breakintoprogram/pico-mposite/images/breadboard.jpeg

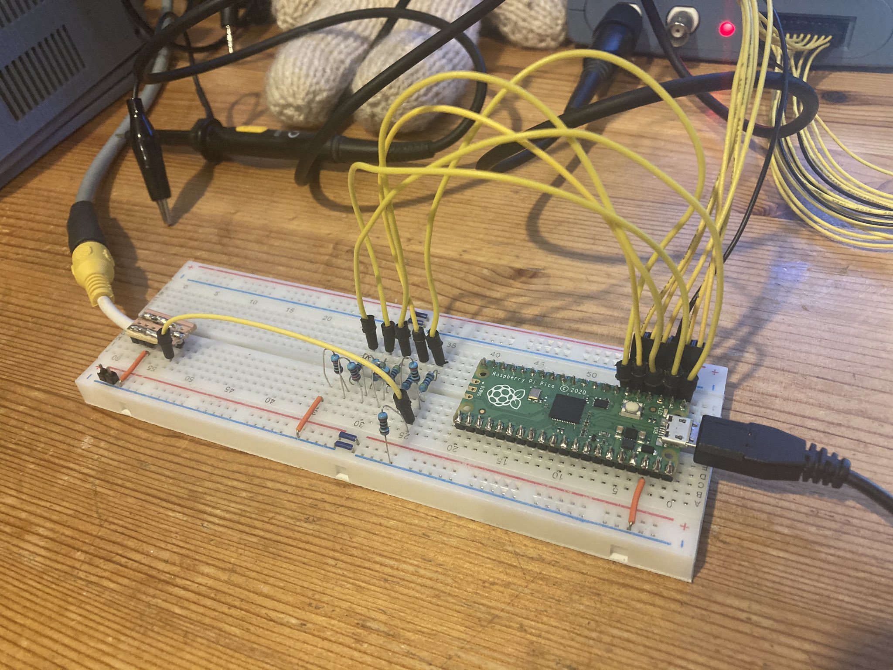
images/breadboard.jpeg
