breakintoprogram/pico-mposite/images/demo_cube.jpeg

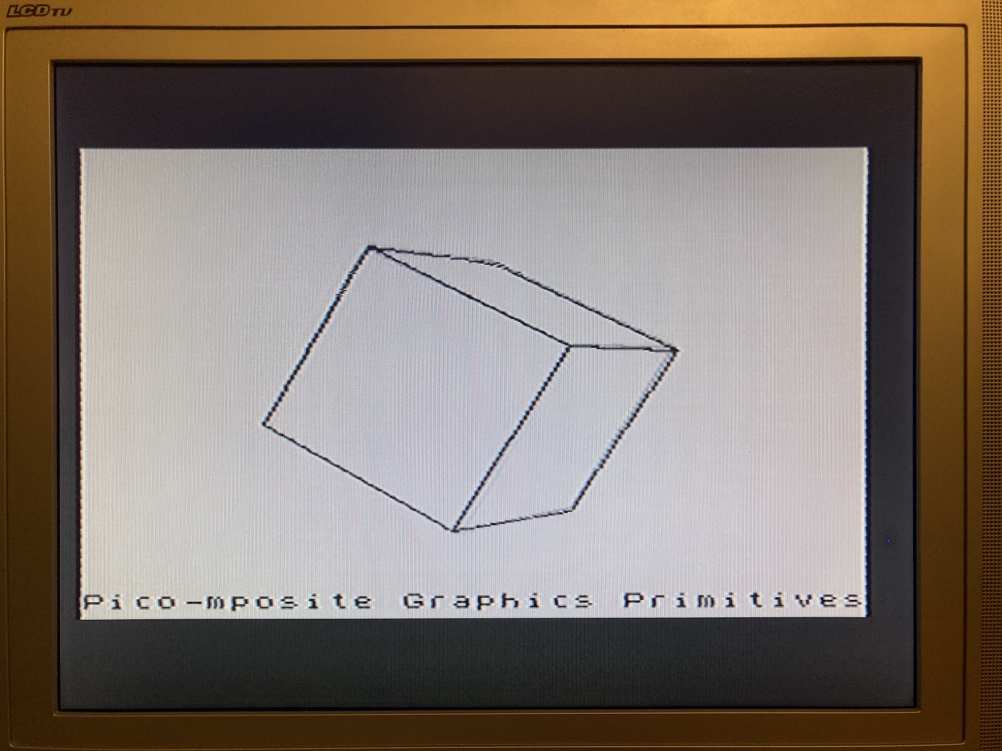
images/demo_cube.jpeg
