breakintoprogram/pico-mposite/images/demo_mandlebrot.jpeg

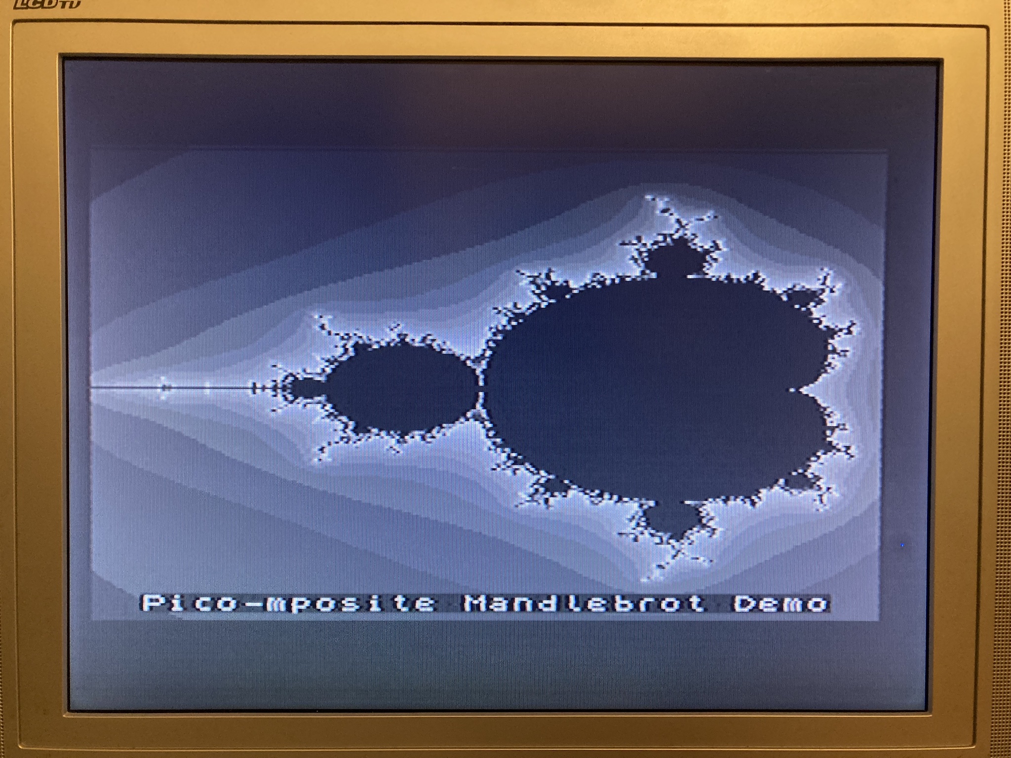
images/demo_mandlebrot.jpeg
