breakintoprogram/pico-mposite/images/demo_mandlebrot_colour.jpeg

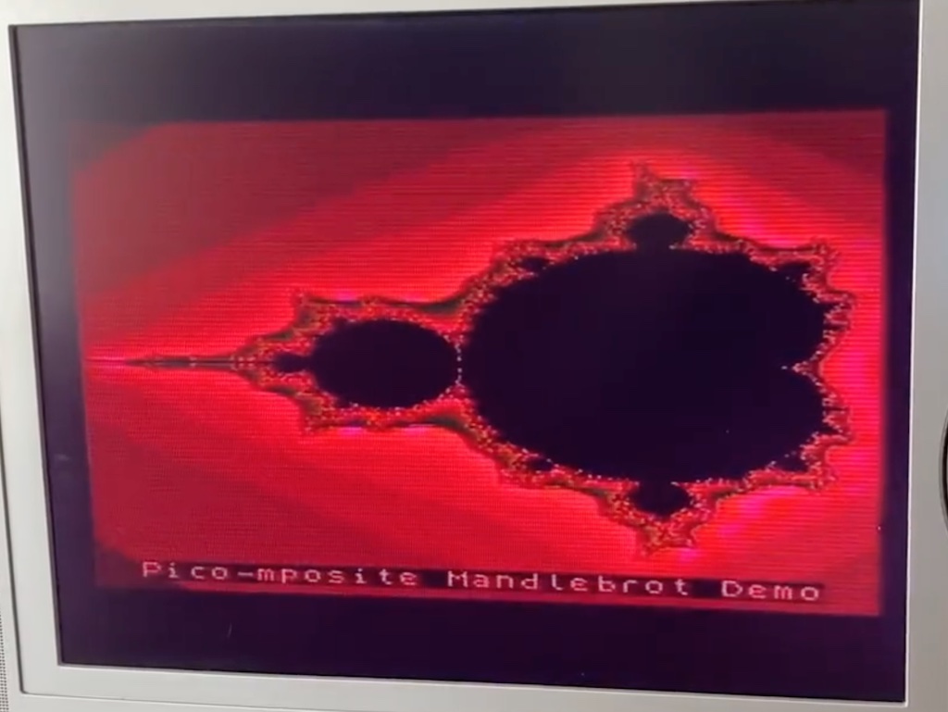
images/demo_mandlebrot_colour.jpeg
