breakintoprogram/pico-mposite/images/video_output.jpeg

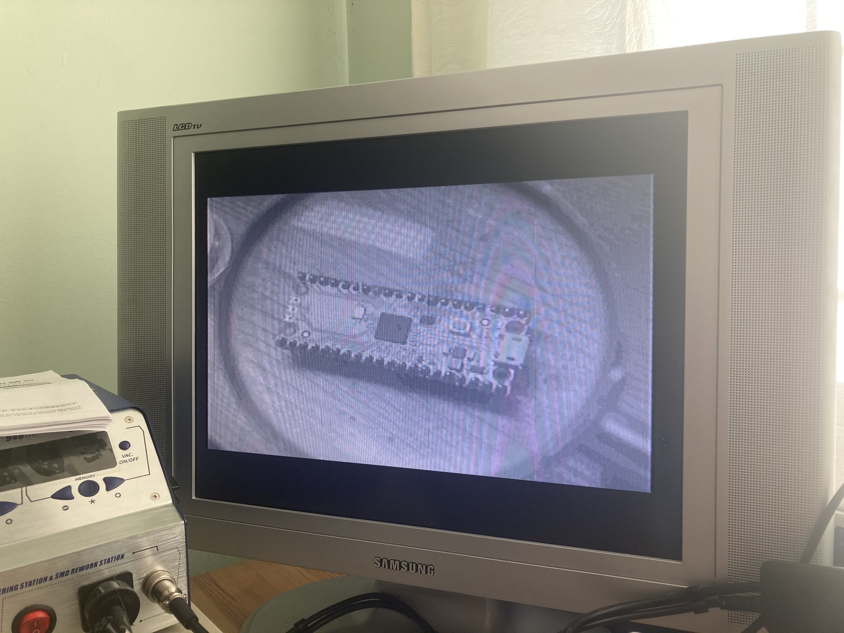
images/video_output.jpeg
