breakintoprogram/pico-mposite/bitmap.c

//
// Title:	        Pico-mposite Demonstration Bitmap
// Author:	        Dean Belfield
// Created:	        12/02/2021
// Last Updated:	01/03/2022
//
// Description:
//
// The monochrome bitmap an array of pixels, where each pixel is a value between 0x10 and 0x1F, giving 16 shades of 
// grey between 0x10 (black) and 0x1F (white). The values correspond to a 5-bit pattern which is converted by the resistor 
// ladder on the Pico GPIO to a voltage output on the composite output of between ~0.5V and 1V
//
// The colour bitmap is an array of pixels, where each pixel is an RGB value, with the bits being arranged as RRRGGGBB
//
// Modinfo:
// 01/02/2022:      Renamed sample_bitmap, made a const, moved to bitmap.c
// 08/02/2022:      Added colour bitmap
// 20/02/2022:      Removed reference to graphics.h
// 01/03/2022:      Fixed colour bitmap

#include "bitmap.h"

#if opt_colour == 0 

unsigned char const sample_bitmap[192][256] = {
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
};

#endif
