breakintoprogram/pico-mposite/config.h

//
// Title:	        Pico-mposite Defines
// Author:	        Dean Belfield
// Created:	        01/03/2022
// Last Updated:	27/09/2024
//
// Modinfo:
// 27//09/2024:		Version 1.3

#pragma once

#define version         "1.3"
#define opt_colour      0       // Set to 0 for monochrome board, 1 for colour board
#define opt_terminal    0       // Set to 1 to just run the terminal software after boot screen
