breakintoprogram/pico-mposite/charset.c

//
// Title:	        Spectrum Character Set
// Author:	        
// Created:	        01/02/2022
// Last Updated:	01/02/2022
//
// Description:
//
// Taken from the 48K rom
//
// Modinfo:
// 

unsigned char const charset[768] = {
	0x00, 0x00, 0x00, 0x00, 0x00, 0x00, 0x00, 0x00,
	0x00, 0x10, 0x10, 0x10, 0x10, 0x00, 0x10, 0x00,
	0x00, 0x24, 0x24, 0x00, 0x00, 0x00, 0x00, 0x00,
	0x00, 0x24, 0x7e, 0x24, 0x24, 0x7e, 0x24, 0x00,
	0x00, 0x08, 0x3e, 0x28, 0x3e, 0x0a, 0x3e, 0x08,
	0x00, 0x62, 0x64, 0x08, 0x10, 0x26, 0x46, 0x00,
	0x00, 0x10, 0x28, 0x10, 0x2a, 0x44, 0x3a, 0x00,
	0x00, 0x08, 0x10, 0x00, 0x00, 0x00, 0x00, 0x00,
	0x00, 0x04, 0x08, 0x08, 0x08, 0x08, 0x04, 0x00,
	0x00, 0x20, 0x10, 0x10, 0x10, 0x10, 0x20, 0x00,
	0x00, 0x00, 0x14, 0x08, 0x3e, 0x08, 0x14, 0x00,
	0x00, 0x00, 0x08, 0x08, 0x3e, 0x08, 0x08, 0x00,
	0x00, 0x00, 0x00, 0x00, 0x00, 0x08, 0x08, 0x10,
	0x00, 0x00, 0x00, 0x00, 0x3e, 0x00, 0x00, 0x00,
	0x00, 0x00, 0x00, 0x00, 0x00, 0x18, 0x18, 0x00,
	0x00, 0x00, 0x02, 0x04, 0x08, 0x10, 0x20, 0x00,
	0x00, 0x3c, 0x46, 0x4a, 0x52, 0x62, 0x3c, 0x00,
	0x00, 0x18, 0x28, 0x08, 0x08, 0x08, 0x3e, 0x00,
	0x00, 0x3c, 0x42, 0x02, 0x3c, 0x40, 0x7e, 0x00,
	0x00, 0x3c, 0x42, 0x0c, 0x02, 0x42, 0x3c, 0x00,
	0x00, 0x08, 0x18, 0x28, 0x48, 0x7e, 0x08, 0x00,
	0x00, 0x7e, 0x40, 0x7c, 0x02, 0x42, 0x3c, 0x00,
	0x00, 0x3c, 0x40, 0x7c, 0x42, 0x42, 0x3c, 0x00,
	0x00, 0x7e, 0x02, 0x04, 0x08, 0x10, 0x10, 0x00,
	0x00, 0x3c, 0x42, 0x3c, 0x42, 0x42, 0x3c, 0x00,
	0x00, 0x3c, 0x42, 0x42, 0x3e, 0x02, 0x3c, 0x00,
	0x00, 0x00, 0x00, 0x10, 0x00, 0x00, 0x10, 0x00,
	0x00, 0x00, 0x10, 0x00, 0x00, 0x10, 0x10, 0x20,
	0x00, 0x00, 0x04, 0x08, 0x10, 0x08, 0x04, 0x00,
	0x00, 0x00, 0x00, 0x3e, 0x00, 0x3e, 0x00, 0x00,
	0x00, 0x00, 0x10, 0x08, 0x04, 0x08, 0x10, 0x00,
	0x00, 0x3c, 0x42, 0x04, 0x08, 0x00, 0x08, 0x00,
	0x00, 0x3c, 0x4a, 0x56, 0x5e, 0x40, 0x3c, 0x00,
	0x00, 0x3c, 0x42, 0x42, 0x7e, 0x42, 0x42, 0x00,
	0x00, 0x7c, 0x42, 0x7c, 0x42, 0x42, 0x7c, 0x00,
	0x00, 0x3c, 0x42, 0x40, 0x40, 0x42, 0x3c, 0x00,
	0x00, 0x78, 0x44, 0x42, 0x42, 0x44, 0x78, 0x00,
	0x00, 0x7e, 0x40, 0x7c, 0x40, 0x40, 0x7e, 0x00,
	0x00, 0x7e, 0x40, 0x7c, 0x40, 0x40, 0x40, 0x00,
	0x00, 0x3c, 0x42, 0x40, 0x4e, 0x42, 0x3c, 0x00,
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
};
