breakintoprogram/pico-mposite/bitmap.h

//
// Title:	        Pico-mposite Demonstration Bitmap
// Author:	        Dean Belfield
// Created:	        01/02/2022
// Last Updated:	26/02/2024
//
// Description:
//
// Modinfo:
// 20/02/2022:      Removed reference to graphics.h
// 26/09/2024:		Externed variables

#pragma once

#include "config.h"

extern unsigned char const sample_bitmap[192][256];
