breakintoprogram/pico-mposite/charset.h

//
// Title:	        Spectrum Character Set
// Author:	        
// Created:	        01/02/2022
// Last Updated:	26/09/2024
//
// Description:
//
// Taken from the Spectrum 48K rom
//
// Modinfo:
// 26/09/2024:		Externed variables

#pragma once

extern unsigned char const charset[768];
